mayjs/maykb_g4/cad/case/right/coordinates.scad

function kb_footprint_centers_right() = [
    [107.9625,98.68],
    [122.25,79.63],
    [136.5375,117.73],
    [207.975,117.73],
    [227.025,117.73],
    [127.0125,98.68],
    [84.15,79.63],
    [150.825,60.58],
    [227.025,98.68],
    [227.025,136.78],
    [112.725,60.58],
    [169.875,60.58],
    [188.925,136.78],
    [55.575,60.58],
    [117.4875,117.73],
    [50.8125,98.68],
    [98.4375,117.73],
    [227.025,79.63],
    [146.0625,98.68],
    [93.675,60.58],
    [196.143099,98.68],
    [65.1,79.63],
    [179.4,79.63],
    [160.35,79.63],
    [155.5875,136.78],
    [79.3875,117.73],
    [103.2,79.63],
    [117.4875,136.78],
    [165.1125,98.68],
    [198.45,60.58],
    [74.625,60.58],
    [155.5875,117.73],
    [69.8625,136.78],
    [88.9125,98.68],
    [60.3375,117.73],
    [69.8625,98.68],
    [141.3,79.63],
    [131.775,60.58],
    [98.4375,136.78],
    [227.025,60.58],
    [203.213,79.63],
    [181.7815,117.73],
    [207.975,136.78],
    [136.5375,136.78],
];

function kb_mount_centers_right() = [
    [124.7,132.45],
    [214.3,112.8],
    [47.75,45.05],
    [166.35,125.1],
    [86.3,133.2],
    [189.9,77.25],
    [231.4,152.55],
    [50.95,152.75],
    [214.15,77.65],
    [72.05,76.0],
    [173.05,112.45],
    [229.8,45.05],
    [110.25,75.85],
];

function audio_jack_x_right() = [
    216.2544,
    61.084957,
];

function usb_c_x_right() = [
    98.930925,
];
